lil-shan/pixy/case/deck_view.png

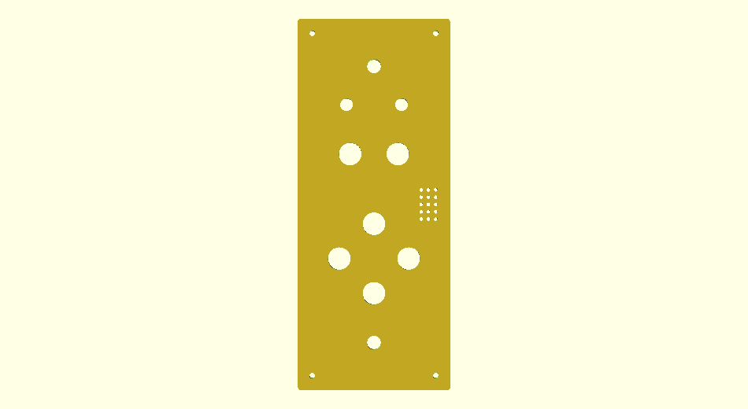
case/deck_view.png
