lil-shan/pixy/docs/img/screens/console-home.jpeg

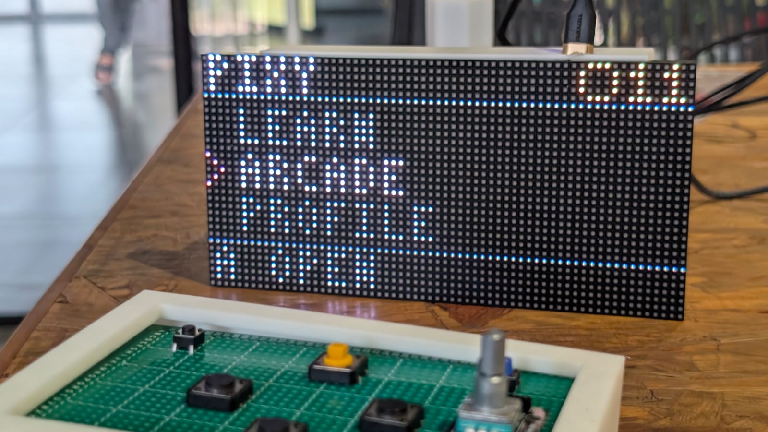
docs/img/screens/console-home.jpeg
