lil-shan/pixy/docs/img/screens/gates.jpeg

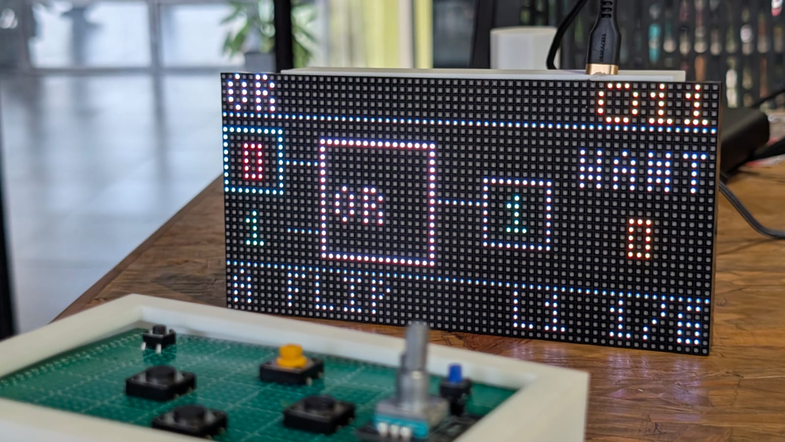
docs/img/screens/gates.jpeg
