lil-shan/pixy/docs/img/screens/gearlab-close.jpeg

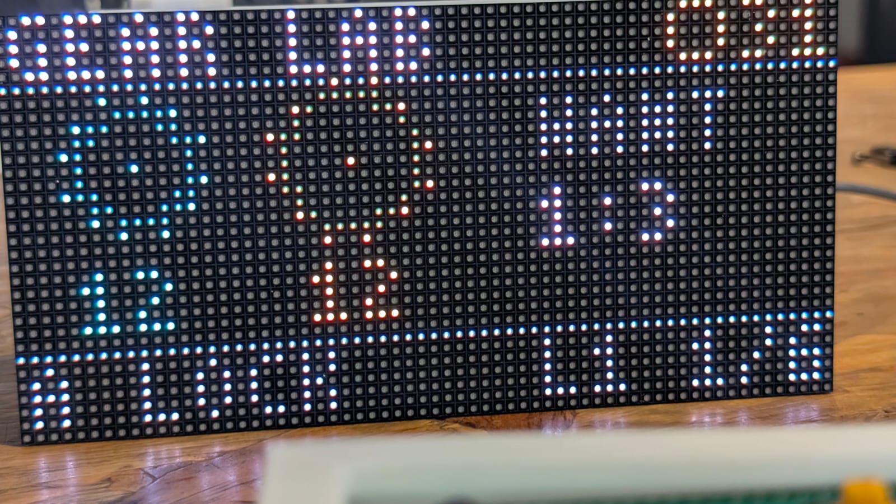
docs/img/screens/gearlab-close.jpeg
