lil-shan/pixy/docs/img/screens/gearlab.jpeg

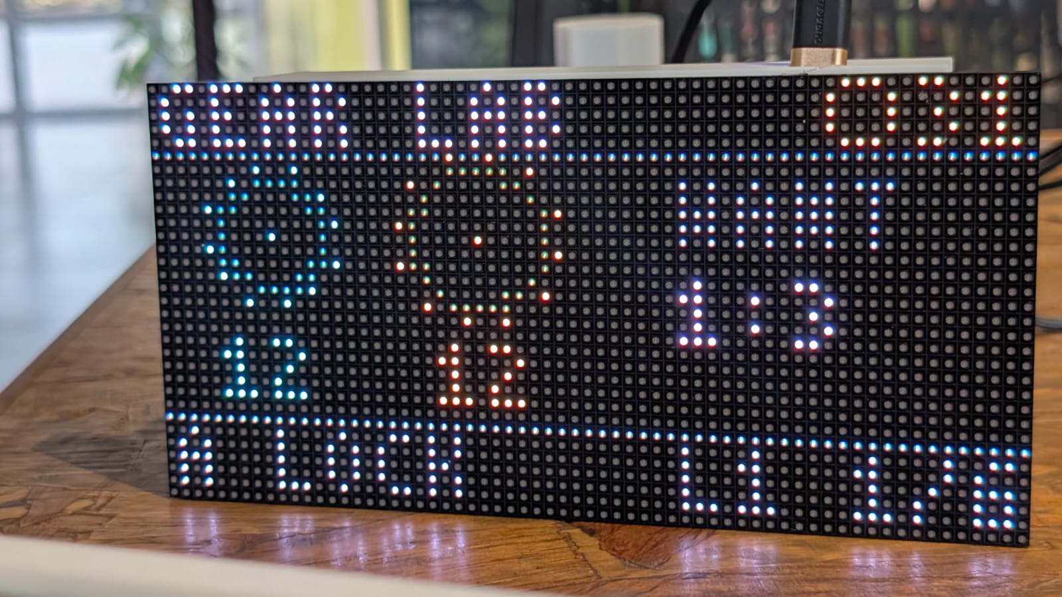
docs/img/screens/gearlab.jpeg
