lil-shan/pixy/docs/img/screens/home.jpeg

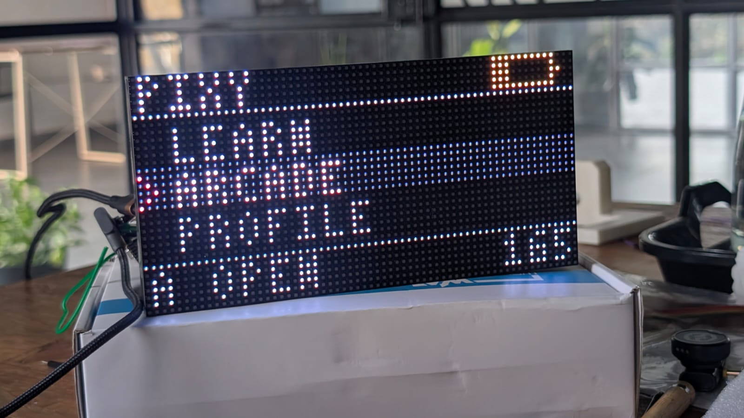
docs/img/screens/home.jpeg
